garyStofer/ARuniMKII/Pictures/IMG_1568.JPG

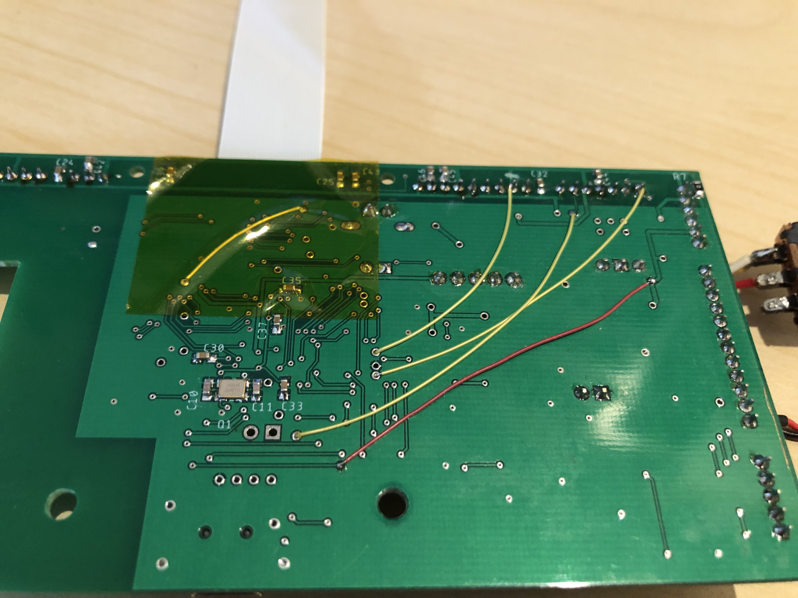
Pictures/IMG_1568.JPG
