garyStofer/ARuniMKII/Pictures/IMG_1569.JPG

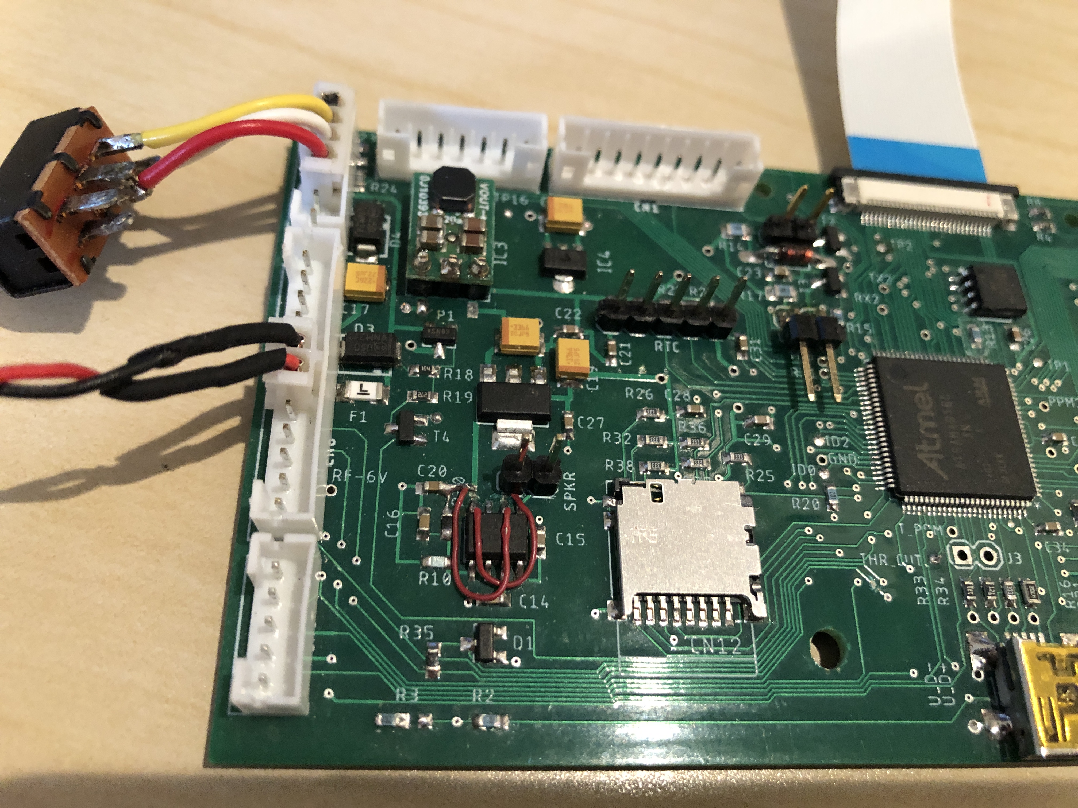
Pictures/IMG_1569.JPG
