garyStofer/ARuniMKII/Pictures/IMG_1572.JPG

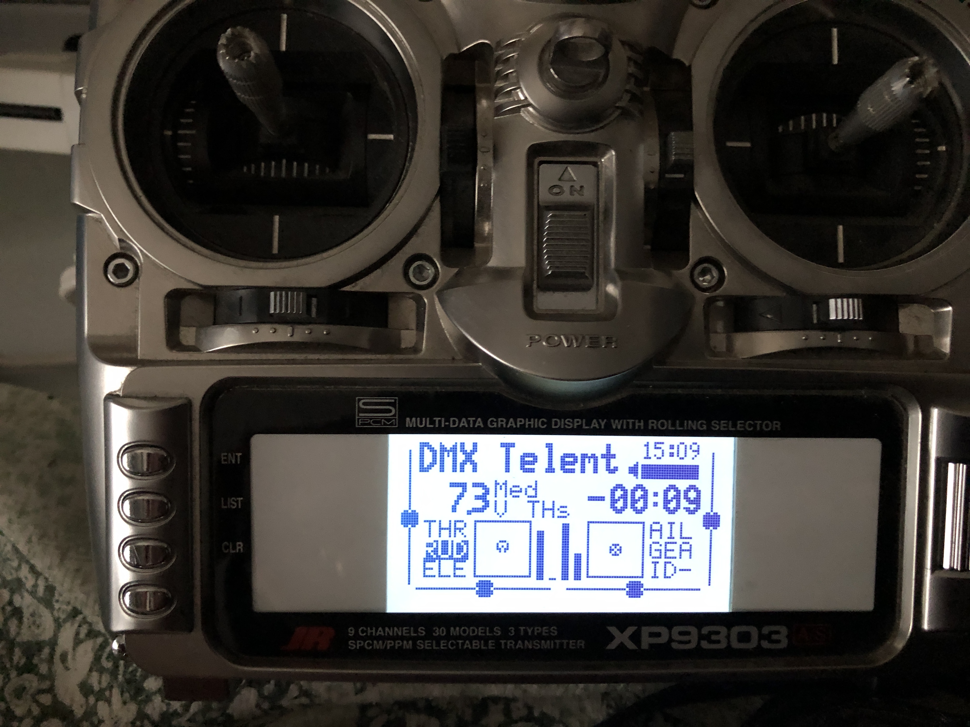
Pictures/IMG_1572.JPG
