garyStofer/ARuniMKII/Pictures/IMG_1574.JPG

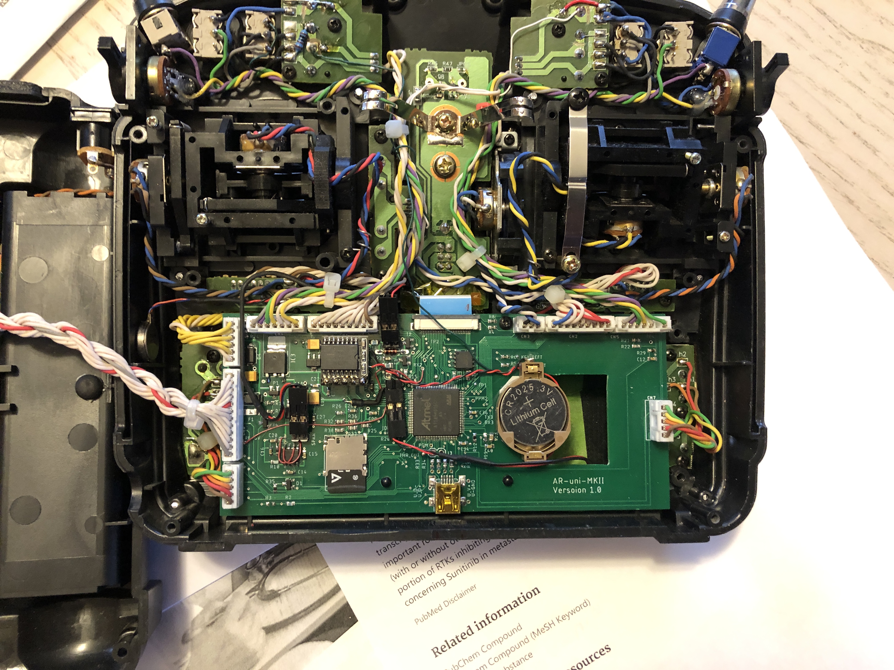
Pictures/IMG_1574.JPG
