garyStofer/ARuniMKII/Pictures/IMG_1575.JPG

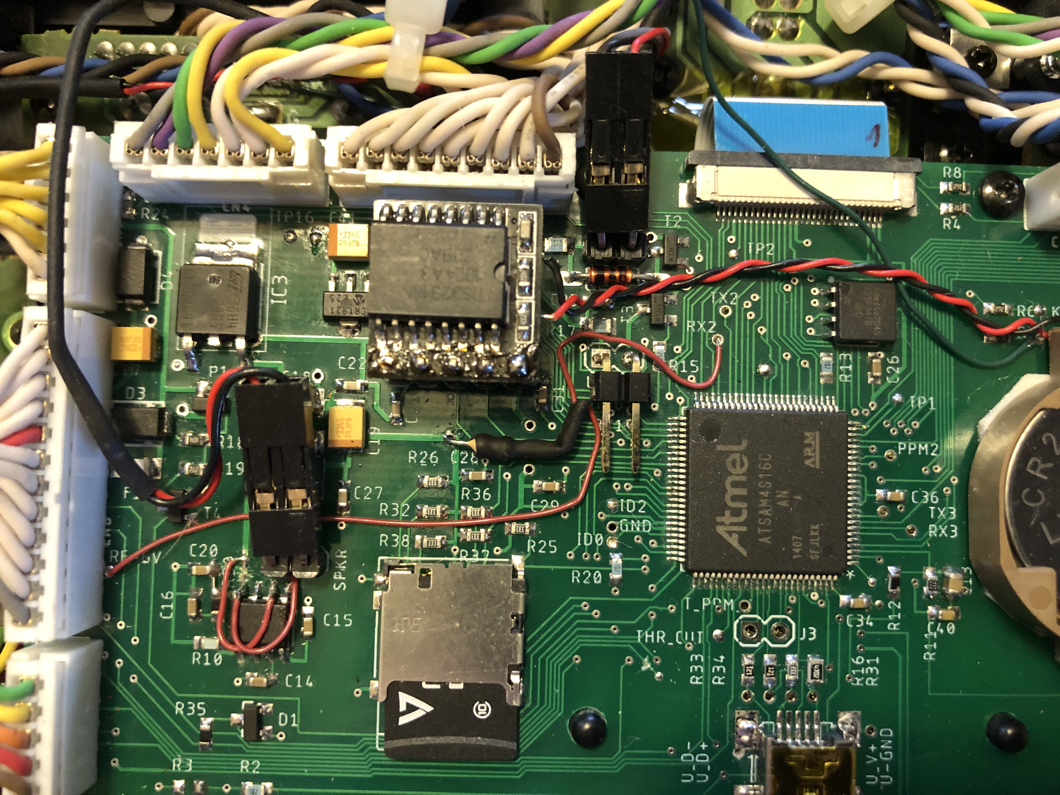
Pictures/IMG_1575.JPG
