garyStofer/ARuniMKII/Pictures/IMG_1577.JPG

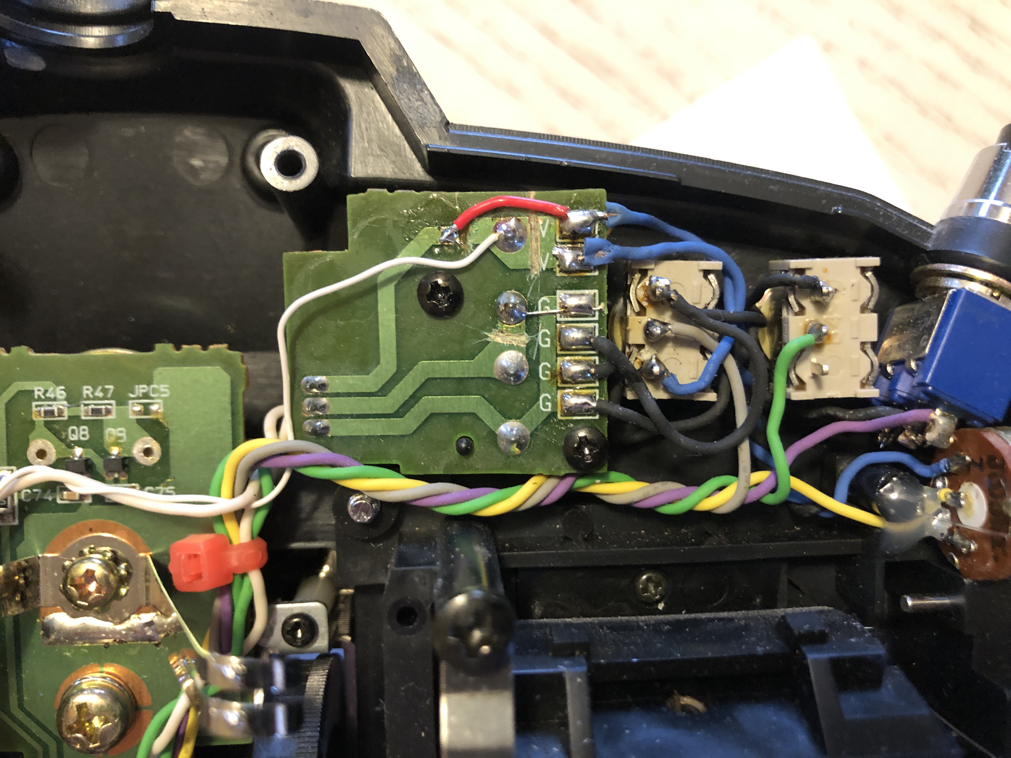
Pictures/IMG_1577.JPG
