garyStofer/ARuniMKII/Pictures/IMG_1578.JPG

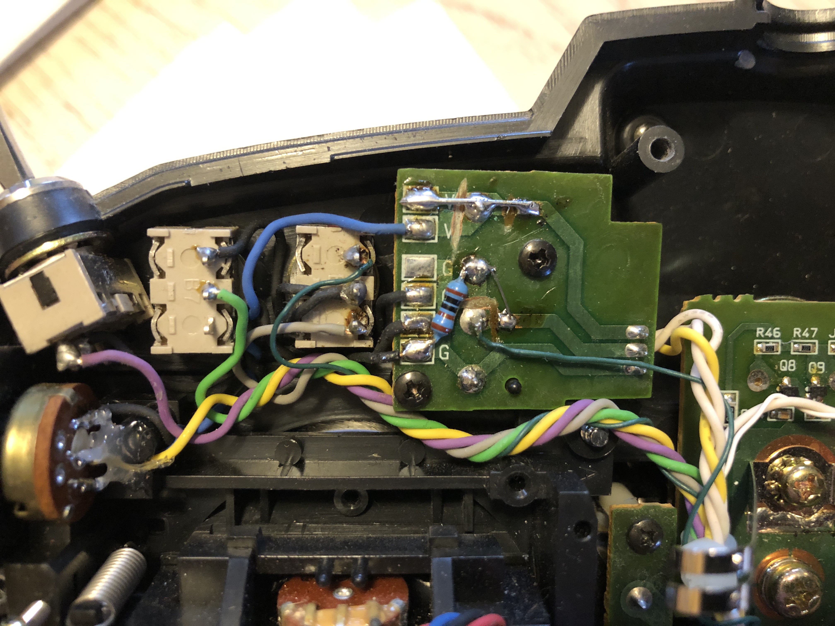
Pictures/IMG_1578.JPG
